poojithas956/Magnum-60/img/1772885072299-qawc8s.png

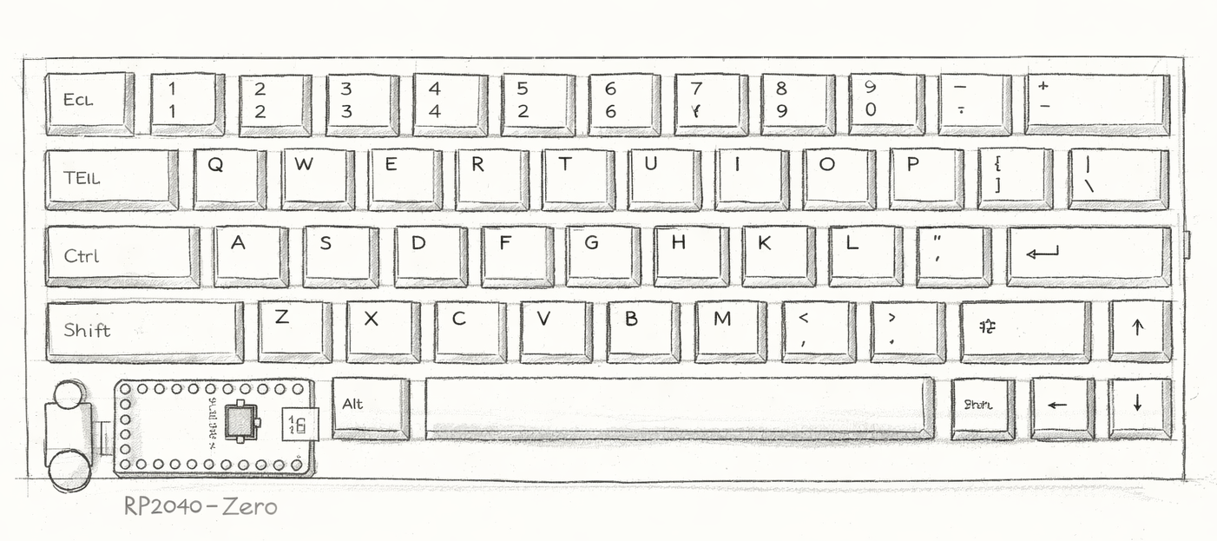
img/1772885072299-qawc8s.png
