poojithas956/Magnum-60/img/1772885123124-k74yzv.png

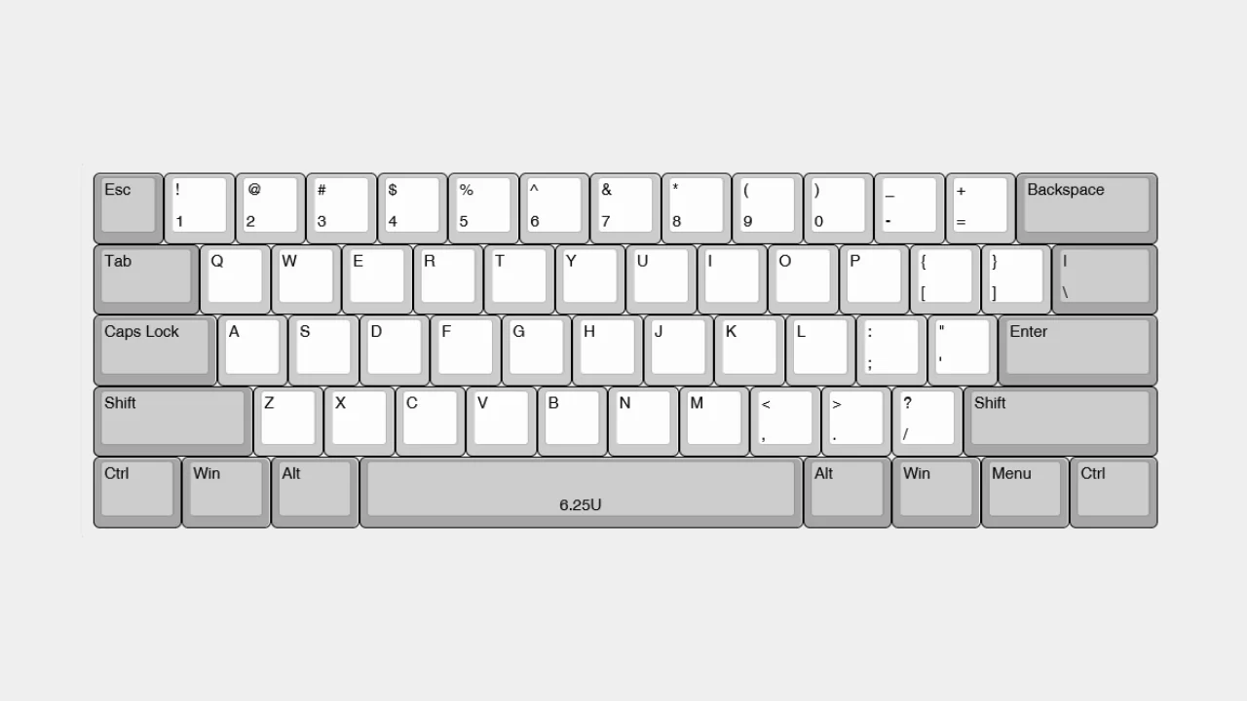
img/1772885123124-k74yzv.png
