poojithas956/Magnum-60/img/1773063967447-ok0iid.jpg

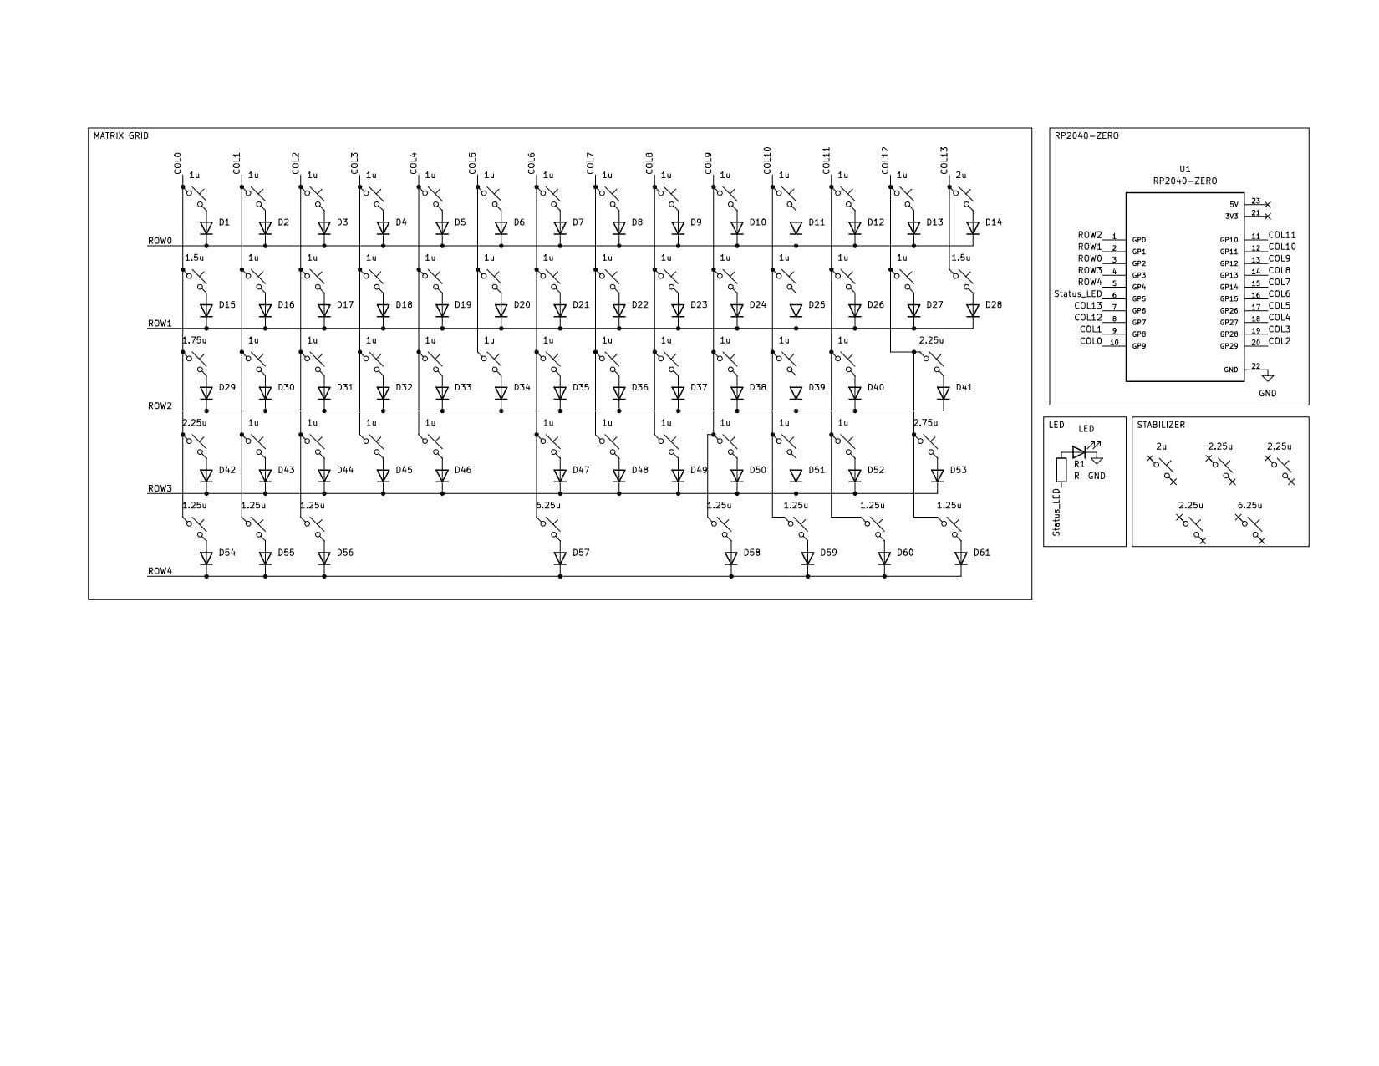
img/1773063967447-ok0iid.jpg
