poojithas956/Magnum-60/img/1773064710980-39x0n3.png

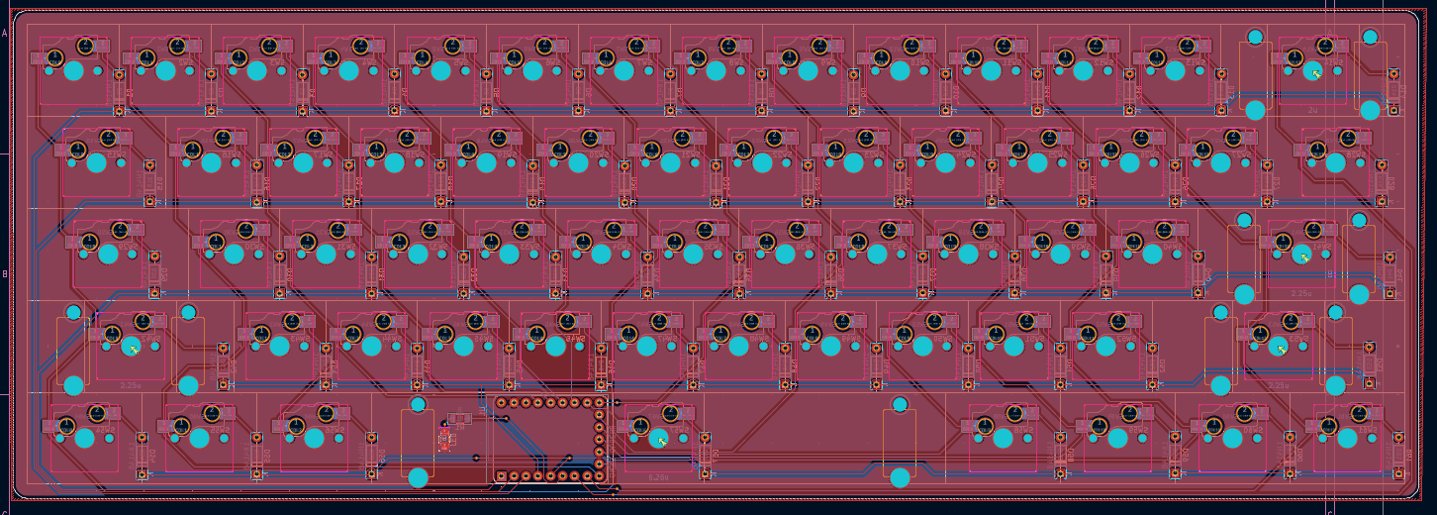
img/1773064710980-39x0n3.png
