poojithas956/Magnum-60/img/1773064746564-ob19ha.png

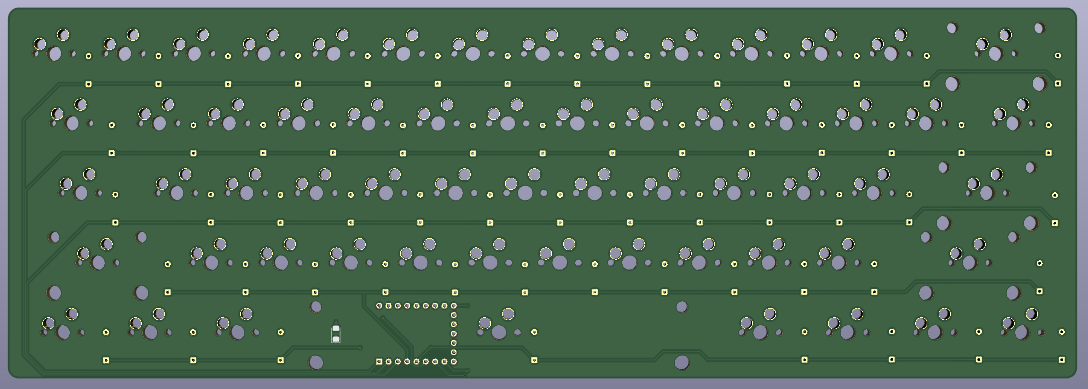
img/1773064746564-ob19ha.png
