poojithas956/Magnum-60/img/1773320307256-ipnhsn.png

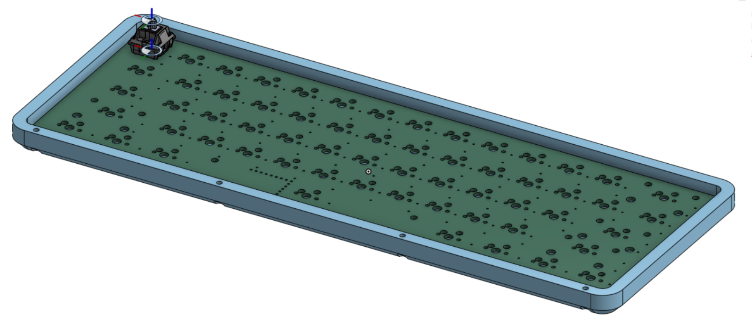
img/1773320307256-ipnhsn.png
