poojithas956/Magnum-60/img/1774181983353-zl58ma.png

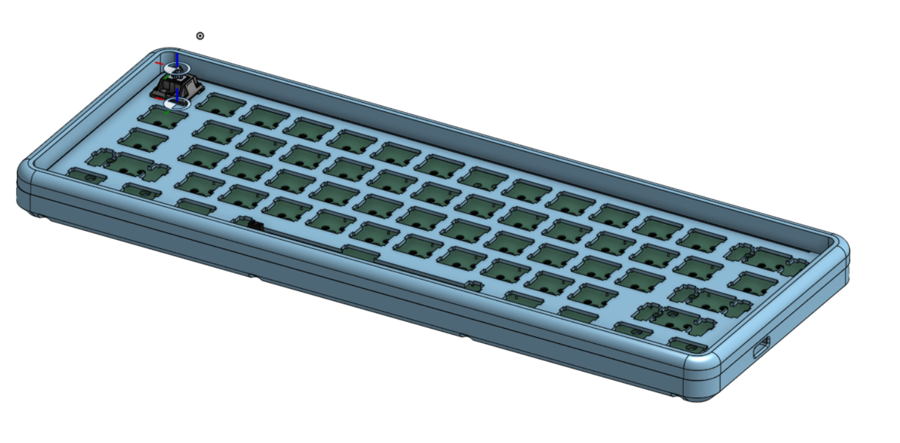
img/1774181983353-zl58ma.png
