poojithas956/Magnum-60/img/1774182138547-1g5pid.png

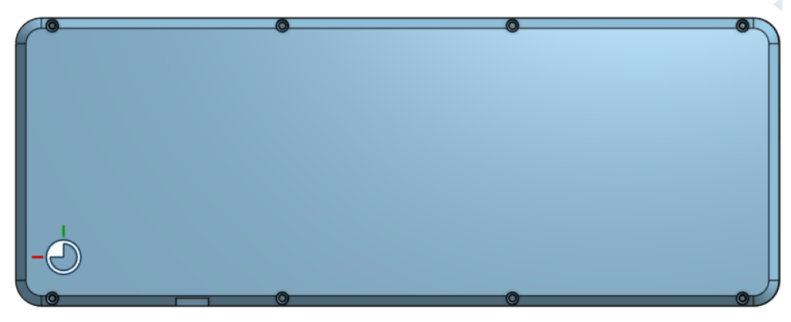
img/1774182138547-1g5pid.png
