poojithas956/Magnum-60/img/1774182173133-1pb0pw.png

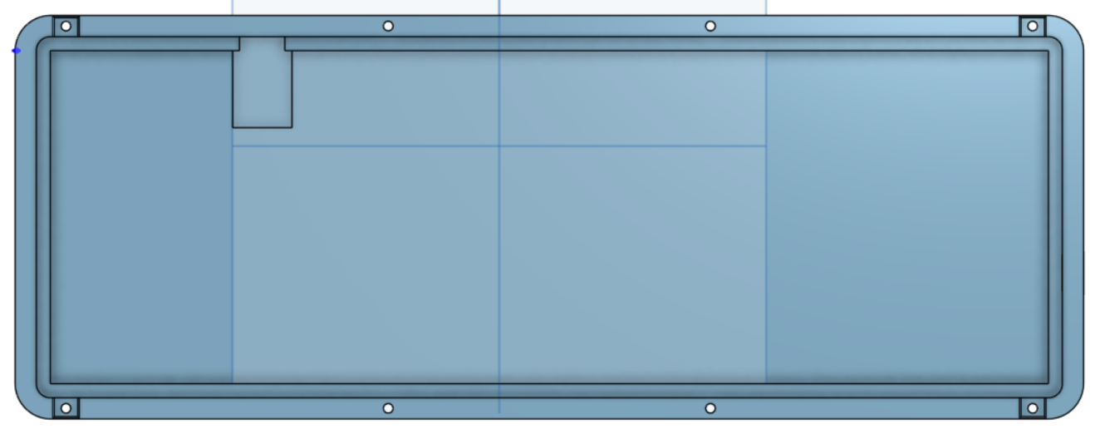
img/1774182173133-1pb0pw.png
