poojithas956/Magnum-60/img/1774183797243-9diazc.png

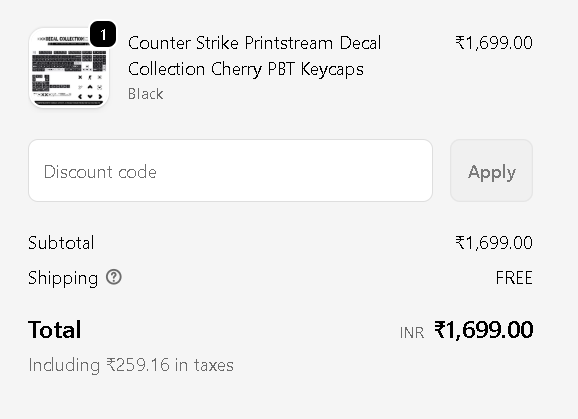
img/1774183797243-9diazc.png
