poojithas956/Magnum-60/img/1774183975837-w6prx8.png

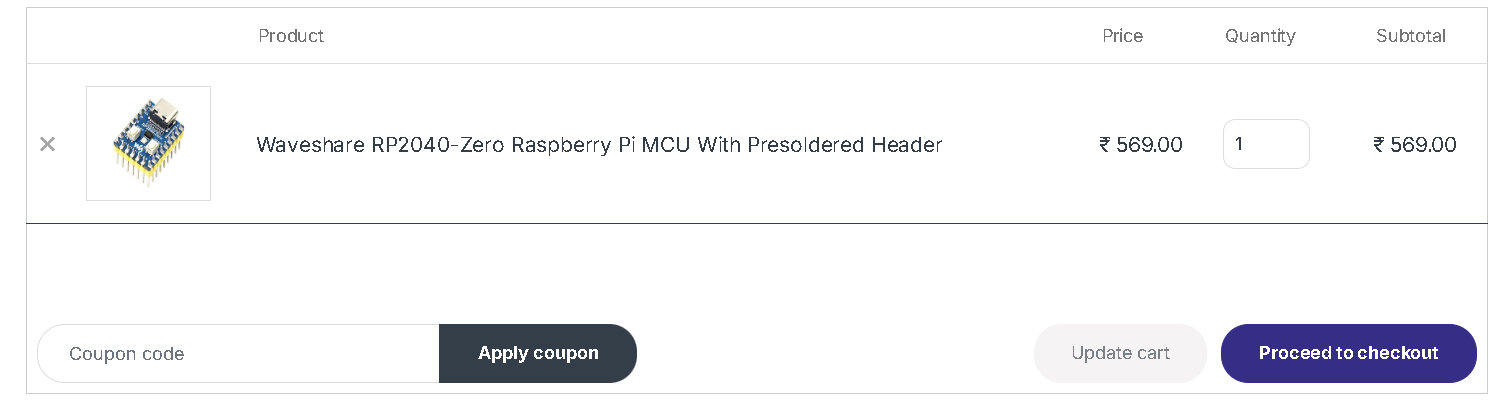
img/1774183975837-w6prx8.png
