poojithas956/Magnum-60/img/1774184284653-p8t0t6.png

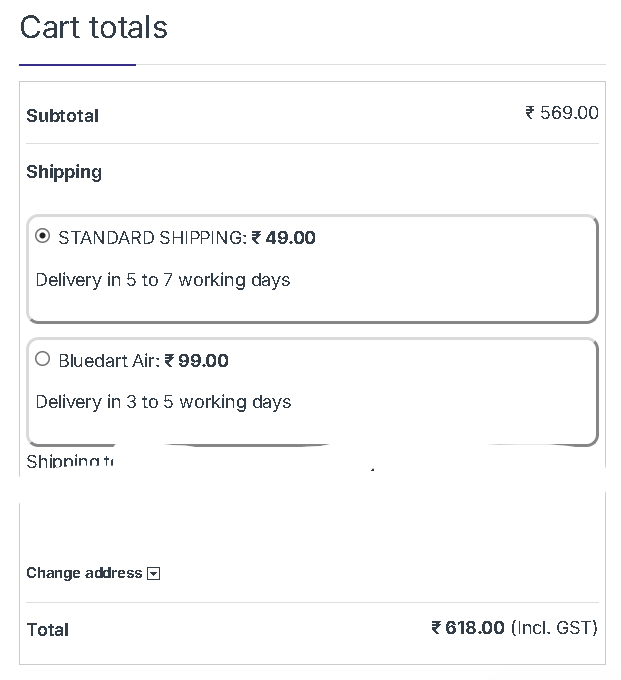
img/1774184284653-p8t0t6.png
