poojithas956/Magnum-60/img/1774184832410-06evmu.png

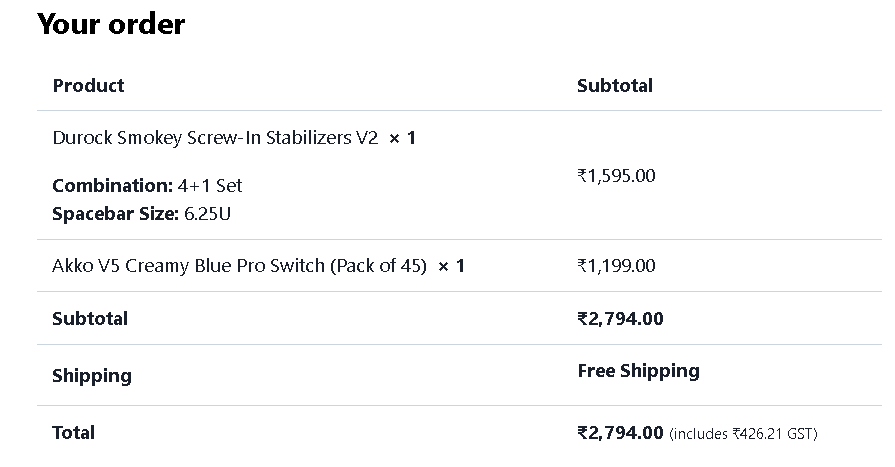
img/1774184832410-06evmu.png
