poojithas956/Magnum-60/img/1774185380367-cz6ysa.png

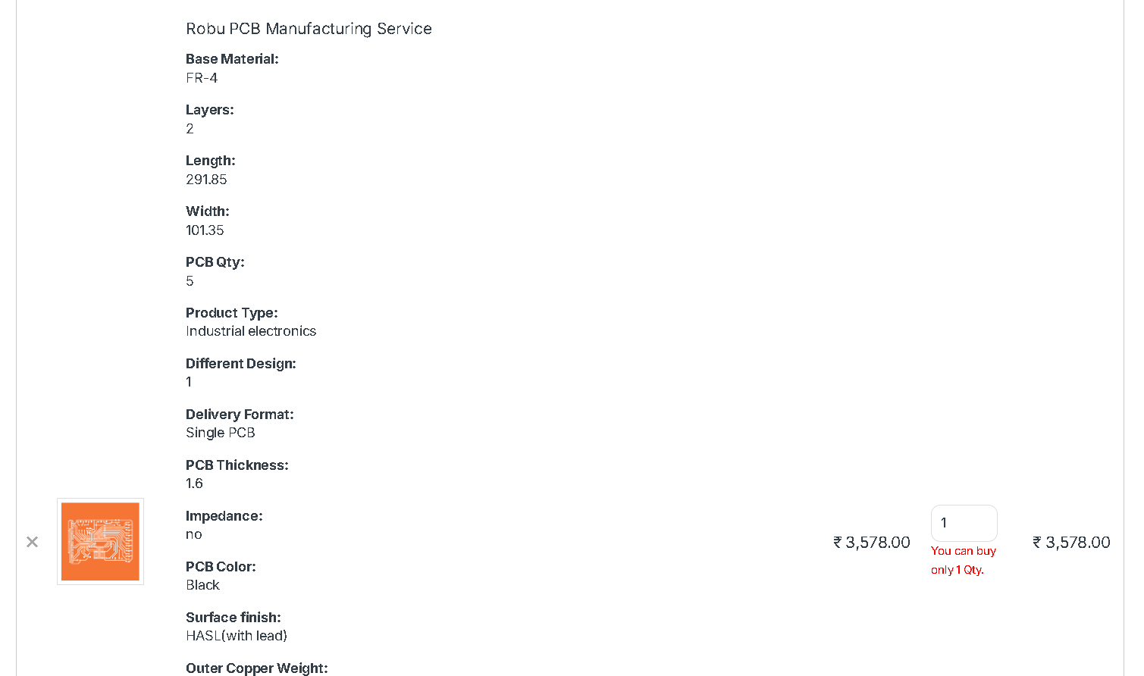
img/1774185380367-cz6ysa.png
