poojithas956/Magnum-60/img/1774185427526-do8u4t.png

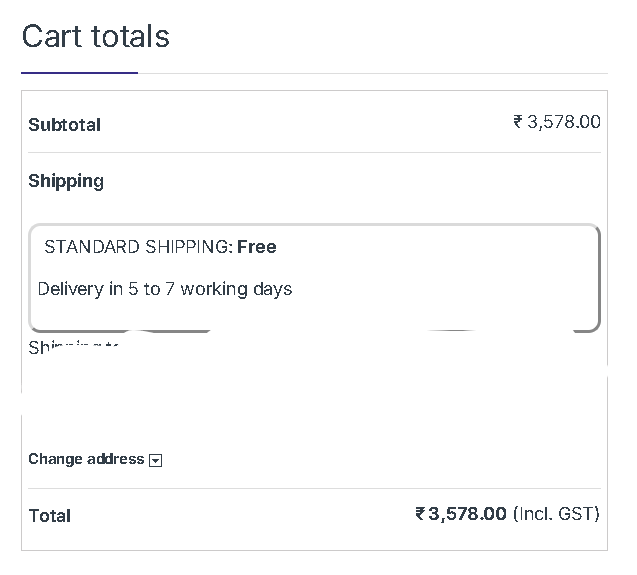
img/1774185427526-do8u4t.png
