poojithas956/Magnum-60/img/1775487881619-3tpr0s.png

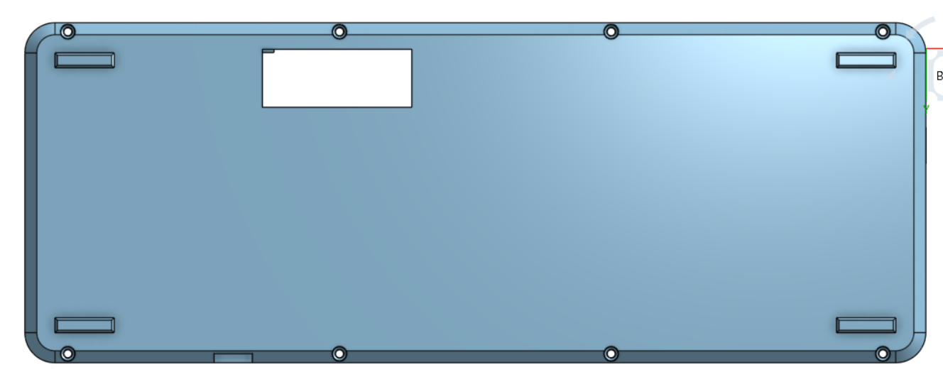
img/1775487881619-3tpr0s.png
